rundb/dictofun/firmware/src/targets/dictofun/tasks/systemstate/task_state.h

// SPDX-License-Identifier:  Apache-2.0
/*
 * Copyright (c) 2022, Roman Turkin
 */
#pragma once

#include "FreeRTOS.h"
#include "boards.h"
#include "queue.h"
#include "timers.h"

#include "nvconfig.h"

namespace systemstate
{
void task_system_state(void* context);

// Set of states that define high-level behavior of the system. 
// Basically corresponds to the particular indication colors.
enum class SystemState: uint8_t
{
    INIT = 0,
    BATTERY_LOW = 1,
    DEVELOPMENT_MODE = 2,
    RECORD_PREPARE = 3,
    RECORDING = 4,
    RECORD_END = 5,
    BLE_OPERATION = 6,
    OUT_OF_MEMORY = 16,
    MEMORY_IS_CORRUPT = 17,
    SHUTDOWN = 32
};

struct Context
{
    QueueHandle_t cli_commands_handle{nullptr};
    QueueHandle_t cli_status_handle{nullptr};

    QueueHandle_t audio_commands_handle{nullptr};
    QueueHandle_t audio_status_handle{nullptr};

    QueueHandle_t memory_commands_handle{nullptr};
    QueueHandle_t memory_status_handle{nullptr};
    QueueHandle_t memory_event_handle{nullptr};

    QueueHandle_t audio_tester_commands_handle{nullptr};

    QueueHandle_t ble_commands_handle{nullptr};
    QueueHandle_t ble_requests_handle{nullptr};
    QueueHandle_t ble_keepalive_handle{nullptr};

    QueueHandle_t led_commands_handle{nullptr};

    QueueHandle_t button_events_handle{nullptr};
    QueueHandle_t button_requests_handle{nullptr};
    QueueHandle_t button_response_handle{nullptr};

    QueueHandle_t battery_measurements_handle{nullptr};
    QueueHandle_t battery_level_to_ble_handle{nullptr};

    TimerHandle_t record_timer_handle{nullptr};

    bool is_record_active{false};
    bool should_record_be_stored{false};
    bool is_ble_system_active{false};
    bool is_shutdown_demanded{false};
    bool is_battery_low{false};
    bool has_operation_timeout_expired{false};

    enum class MemoryStatus
    {
        BUSY,
        READY,
        OUT_OF_MEMORY,
        CORRUPT,
    };
    MemoryStatus memory_status{MemoryStatus::BUSY};

    // This variable tracks the use-case of a record restart before the session end
    uint32_t records_per_launch_counter{0};

    SystemState system_state{SystemState::INIT};

    struct Timestamps
    {
        uint32_t last_record_start_timestamp{timestamp_uninitialized_value};
        uint32_t last_record_end_timestamp{0};
        uint32_t last_ble_activity_timestamp{timestamp_uninitialized_value};
        uint32_t ble_disconnect_event_timestamp{timestamp_uninitialized_value};
        uint32_t shutdown_procedure_start_timestamp{timestamp_uninitialized_value};
        uint32_t low_battery_detected_timestamp{timestamp_uninitialized_value};
        uint32_t memory_issue_detected_timestamp{timestamp_uninitialized_value};

        bool has_start_timestamp_been_updated()
        {
            return last_record_start_timestamp != timestamp_uninitialized_value;
        }
        bool has_disconnect_timestamp_been_updated()
        {
            return ble_disconnect_event_timestamp != timestamp_uninitialized_value;
        }
        bool has_ble_timestamp_been_updated()
        {
            return last_ble_activity_timestamp != timestamp_uninitialized_value;
        }
        bool has_low_batt_detection_timestamp_been_updated()
        {
            return low_battery_detected_timestamp != timestamp_uninitialized_value;
        }
        bool has_memory_issue_detection_timestamp_been_updated()
        {
            return memory_issue_detected_timestamp != timestamp_uninitialized_value;
        }
        void reset()
        {
            last_ble_activity_timestamp = timestamp_uninitialized_value;
            ble_disconnect_event_timestamp = timestamp_uninitialized_value;
        }

    private:
        static constexpr uint32_t timestamp_uninitialized_value{0xaf1bfb98};
    };
    Timestamps timestamps;
};

void record_end_callback(TimerHandle_t timer);

void launch_cli_command_record(Context& context,
                               const uint32_t duration,
                               bool should_store_the_record);
void launch_cli_command_memory_test(Context& context, const uint32_t test_id, const uint32_t range_start, const uint32_t range_end);
void launch_cli_command_ble_operation(Context& context, const uint32_t command_id);
void launch_cli_command_system(Context& context, const uint32_t command_id);
void launch_cli_command_opmode(Context& context,
                               const uint32_t mode_id,
                               application::NvConfig& nvc);
void launch_cli_command_led(Context& context, const uint32_t color_id, const uint32_t mode_id);

void load_nvconfig(Context& context);
application::Mode get_operation_mode();
bool is_record_start_by_cli_allowed(Context& context);
result::Result launch_record_timer(const TickType_t record_duration, Context& context);

void shutdown_ldo();
void configure_power_latch();
bool process_timeouts(Context& context);
result::Result enable_ble_subsystem(Context& context);
result::Result disable_ble_subsystem(Context& context);

result::Result request_record_creation(const Context& context);
result::Result request_record_start(Context& context);
result::Result request_record_stop(const Context& context);
result::Result request_record_closure(const Context& context);

} // namespace systemstate
