rundb/dictofun/firmware/src/targets/dictofun/BleSystem.cpp

// SPDX-License-Identifier:  Apache-2.0
/*
 * Copyright (c) 2022, Roman Turkin
 */

#include "BleSystem.h"
#include <softdevice/common/nrf_sdh.h>
#include <softdevice/common/nrf_sdh_ble.h>
#include <ble/nrf_ble_qwr/nrf_ble_qwr.h>
#include <ble/nrf_ble_gatt/nrf_ble_gatt.h>
#include <ble/ble_services/ble_lbs/ble_lbs.h>
#include <ble/common/ble_advdata.h>
#include <ble/common/ble_conn_params.h>
#include <ble/peer_manager/peer_manager_handler.h>
#include <libraries/util/app_error.h>
#include "ble_file_transfer_service.h"
#include <nrf_log.h>
#include <stdint.h>
#include "BleServices.h"
#include <boards/boards.h>
#include "simple_fs.h"

// Legacy define. I haven't come up with a replacement for this part of nordic interfaces
// NRF_BLE_QWR_DEF(m_qwr);
//BLE_LBS_DEF(m_lbs);                                                             /**< LED Button Service instance. */
BLE_FTS_DEF(m_fts, NRF_SDH_BLE_TOTAL_LINK_COUNT);

#define APP_ADV_INTERVAL                200                                      /**< The advertising interval (in units of 0.625 ms; this value corresponds to 40 ms). */
#define APP_ADV_DURATION                BLE_GAP_ADV_TIMEOUT_GENERAL_UNLIMITED   /**< The advertising time-out (in units of seconds). When set to 0, we will never time out. */

static uint8_t m_enc_advdata[BLE_GAP_ADV_SET_DATA_SIZE_MAX];                    /**< Buffer for storing an encoded advertising set. */
static uint8_t m_enc_scan_response_data[BLE_GAP_ADV_SET_DATA_SIZE_MAX];         /**< Buffer for storing an encoded scan data. */
static uint8_t m_adv_handle = BLE_GAP_ADV_SET_HANDLE_NOT_SET;                   /**< Advertising handle used to identify an advertising set. */

static ble_gap_adv_data_t m_adv_data =
{
    .adv_data =
    {
        .p_data = m_enc_advdata,
        .len    = BLE_GAP_ADV_SET_DATA_SIZE_MAX
    },
    .scan_rsp_data =
    {
        .p_data = m_enc_scan_response_data,
        .len    = BLE_GAP_ADV_SET_DATA_SIZE_MAX

    }
};

static nrf_ble_gatt_t m_gatt;
NRF_SDH_BLE_OBSERVER(m_gatt_obs, NRF_BLE_GATT_BLE_OBSERVER_PRIO, nrf_ble_gatt_on_ble_evt, &m_gatt);


namespace ble
{

BleSystem * BleSystem::_instance{nullptr};
const char BleSystem::DEVICE_NAME[] = BOARD_NAME;

static void services_init();
static void advertising_init();

void BleSystem::init()
{
    initBleStack();
    initGapParams();
    initGatt();
    initBonding();
    _bleServices.init();
    _qwr_default_handle = _bleServices.getQwrHandle();
    advertising_init();
    initConnParameters();
}

void BleSystem::start()
{
    _bleServices.start();
    startAdvertising();
    _isActive = true;
}

void BleSystem::stop()
{
    const auto disconnect_result = sd_ble_gap_disconnect(BleSystem::getInstance().getConnectionHandle(), 
        BLE_HCI_REMOTE_USER_TERMINATED_CONNECTION);
    if (disconnect_result != 0)
    {
        NRF_LOG_WARNING("gap disconnect: err_code = 0x%x", disconnect_result);
    }
    stopAdvertising();
    _isActive = false;
}

void BleSystem::cyclic()
{
    if (_isActive)
    {
        _bleServices.cyclic();
    }
}

void BleSystem::startAdvertising()
{
    ret_code_t           err_code;

    err_code = sd_ble_gap_adv_start(m_adv_handle, APP_BLE_CONN_CFG_TAG);
    //APP_ERROR_CHECK(err_code);
    if (err_code != 0)
    {
        NRF_LOG_WARNING("startAdv: err_code = %d", err_code);
    }
}

void BleSystem::stopAdvertising()
{
    ret_code_t           err_code;

    err_code = sd_ble_gap_adv_stop(m_adv_handle);
    if (err_code != 0)
    {
        NRF_LOG_WARNING("stopAdv: err_code = %d", err_code);
    }
}

void ble_evt_handler(ble_evt_t const * p_ble_evt, void * p_context)
{
    BleSystem::getInstance().bleEventHandler(p_ble_evt, p_context);
}

void BleSystem::bleEventHandler(ble_evt_t const * p_ble_evt, void * p_context)
{
    ret_code_t err_code;
   
    switch (p_ble_evt->header.evt_id)
    {
        case BLE_GAP_EVT_CONNECTED:
            NRF_LOG_INFO("Connected");
            // bsp_board_led_on(CONNECTED_LED);
            // bsp_board_led_off(ADVERTISING_LED);
            m_conn_handle = p_ble_evt->evt.gap_evt.conn_handle;
            err_code = nrf_ble_qwr_conn_handle_assign(_qwr_default_handle, m_conn_handle);
            APP_ERROR_CHECK(err_code);
            break;

        case BLE_GAP_EVT_DISCONNECTED:
            NRF_LOG_INFO("Disconnected");
            //bsp_board_led_off(CONNECTED_LED);
            m_conn_handle = BLE_CONN_HANDLE_INVALID;
            startAdvertising();
            break;

        case BLE_GAP_EVT_SEC_PARAMS_REQUEST:
            NRF_LOG_DEBUG("BLE_GAP_EVT_SEC_PARAMS_REQUEST");
            break;
        
        case BLE_GAP_EVT_AUTH_KEY_REQUEST:
            NRF_LOG_INFO("BLE_GAP_EVT_AUTH_KEY_REQUEST");
            break;

        case BLE_GAP_EVT_LESC_DHKEY_REQUEST:
            NRF_LOG_INFO("BLE_GAP_EVT_LESC_DHKEY_REQUEST");
            break;
       case BLE_GAP_EVT_AUTH_STATUS:
            NRF_LOG_INFO("BLE_GAP_EVT_AUTH_STATUS: status=0x%x bond=0x%x lv4: %d kdist_own:0x%x kdist_peer:0x%x",
                          p_ble_evt->evt.gap_evt.params.auth_status.auth_status,
                          p_ble_evt->evt.gap_evt.params.auth_status.bonded,
                          p_ble_evt->evt.gap_evt.params.auth_status.sm1_levels.lv4,
                          *((uint8_t *)&p_ble_evt->evt.gap_evt.params.auth_status.kdist_own),
                          *((uint8_t *)&p_ble_evt->evt.gap_evt.params.auth_status.kdist_peer));
            break;

        case BLE_GAP_EVT_PHY_UPDATE_REQUEST:
        {
            NRF_LOG_DEBUG("PHY update request.");
            ble_gap_phys_t const phys =
            {
                .tx_phys = BLE_GAP_PHY_AUTO,
                .rx_phys = BLE_GAP_PHY_AUTO,
            };
            err_code = sd_ble_gap_phy_update(p_ble_evt->evt.gap_evt.conn_handle, &phys);
            APP_ERROR_CHECK(err_code);
        } break;

        case BLE_GATTS_EVT_SYS_ATTR_MISSING:
            // No system attributes have been stored.
            err_code = sd_ble_gatts_sys_attr_set(m_conn_handle, NULL, 0, 0);
            APP_ERROR_CHECK(err_code);
            break;

        case BLE_GATTC_EVT_TIMEOUT:
            // Disconnect on GATT Client timeout event.
            NRF_LOG_DEBUG("GATT Client Timeout.");
            err_code = sd_ble_gap_disconnect(p_ble_evt->evt.gattc_evt.conn_handle,
                                             BLE_HCI_REMOTE_USER_TERMINATED_CONNECTION);
            APP_ERROR_CHECK(err_code);
            break;

        case BLE_GATTS_EVT_TIMEOUT:
            // Disconnect on GATT Server timeout event.
            NRF_LOG_DEBUG("GATT Server Timeout.");
            err_code = sd_ble_gap_disconnect(p_ble_evt->evt.gatts_evt.conn_handle,
                                             BLE_HCI_REMOTE_USER_TERMINATED_CONNECTION);
            APP_ERROR_CHECK(err_code);
            break;

        default:
            // No implementation needed.
            break;
    }
}

void BleSystem::initBleStack()
{
    ret_code_t err_code;

    err_code = nrf_sdh_enable_request();
    APP_ERROR_CHECK(err_code);

    // Configure the BLE stack using the default settings.
    // Fetch the start address of the application RAM.
    uint32_t ram_start = 0;
    err_code = nrf_sdh_ble_default_cfg_set(APP_BLE_CONN_CFG_TAG, &ram_start);
    APP_ERROR_CHECK(err_code);

    // Enable BLE stack.
    err_code = nrf_sdh_ble_enable(&ram_start);
    APP_ERROR_CHECK(err_code);

    // Register a handler for BLE events.
    NRF_SDH_BLE_OBSERVER(m_ble_observer, APP_BLE_OBSERVER_PRIO, ble_evt_handler, NULL);    
}

void BleSystem::initGapParams()
{
    ret_code_t              err_code;
    ble_gap_conn_params_t   gap_conn_params;
    ble_gap_conn_sec_mode_t sec_mode;

    BLE_GAP_CONN_SEC_MODE_SET_OPEN(&sec_mode);

    err_code = sd_ble_gap_device_name_set(&sec_mode,
                                          (const uint8_t *)DEVICE_NAME,
                                          strlen(DEVICE_NAME));
    APP_ERROR_CHECK(err_code);

    memset(&gap_conn_params, 0, sizeof(gap_conn_params));

    gap_conn_params.min_conn_interval = MIN_CONN_INTERVAL;
    gap_conn_params.max_conn_interval = MAX_CONN_INTERVAL;
    gap_conn_params.slave_latency     = SLAVE_LATENCY;
    gap_conn_params.conn_sup_timeout  = CONN_SUP_TIMEOUT;

    err_code = sd_ble_gap_ppcp_set(&gap_conn_params);
    APP_ERROR_CHECK(err_code);
}

void BleSystem::initGatt()
{
    ret_code_t err_code = nrf_ble_gatt_init(&m_gatt, NULL);
    APP_ERROR_CHECK(err_code);
}

void BleSystem::bonded_client_add(pm_evt_t const * p_evt)
{
    uint16_t   conn_handle = p_evt->conn_handle;
    uint16_t   peer_id     = p_evt->peer_id;
}

void BleSystem::bonded_client_remove_all()
{
    // TODO: implement
}

void BleSystem::on_bonded_peer_reconnection_lvl_notify(pm_evt_t const * p_evt)
{
    ret_code_t        err_code;
    static uint16_t   peer_id   = PM_PEER_ID_INVALID;

    peer_id = p_evt->peer_id;
}

void BleSystem::pm_evt_handler(pm_evt_t const * p_evt)
{
    pm_handler_on_pm_evt(p_evt);
    pm_handler_disconnect_on_sec_failure(p_evt);
    pm_handler_flash_clean(p_evt);

    switch (p_evt->evt_id)
    {
        case PM_EVT_BONDED_PEER_CONNECTED:
            bonded_client_add(p_evt);
            on_bonded_peer_reconnection_lvl_notify(p_evt);
            break;

        case PM_EVT_CONN_SEC_SUCCEEDED:
            bonded_client_add(p_evt);
            break;

        case PM_EVT_PEERS_DELETE_SUCCEEDED:
            bonded_client_remove_all();

            // Bonds are deleted. Start scanning.
            break;

        default:
            break;
    }
}

void BleSystem::initBonding()
{
    ble_gap_sec_params_t sec_param;
    ret_code_t           err_code;

    err_code = pm_init();
    APP_ERROR_CHECK(err_code);

    memset(&sec_param, 0, sizeof(ble_gap_sec_params_t));

    // Security parameters to be used for all security procedures.
    sec_param.bond           = SEC_PARAM_BOND;
    sec_param.mitm           = SEC_PARAM_MITM;
    sec_param.lesc           = SEC_PARAM_LESC;
    sec_param.keypress       = SEC_PARAM_KEYPRESS;
    sec_param.io_caps        = SEC_PARAM_IO_CAPABILITIES;
    sec_param.oob            = SEC_PARAM_OOB;
    sec_param.min_key_size   = SEC_PARAM_MIN_KEY_SIZE;
    sec_param.max_key_size   = SEC_PARAM_MAX_KEY_SIZE;
    sec_param.kdist_own.enc  = 1;
    sec_param.kdist_own.id   = 1;
    sec_param.kdist_peer.enc = 1;
    sec_param.kdist_peer.id  = 1;

    err_code = pm_sec_params_set(&sec_param);
    APP_ERROR_CHECK(err_code);

    err_code = pm_register(pm_evt_handler);
    APP_ERROR_CHECK(err_code);
}

static void on_conn_params_evt(ble_conn_params_evt_t * p_evt)
{
    ret_code_t err_code;

    if (p_evt->evt_type == BLE_CONN_PARAMS_EVT_FAILED)
    {
        err_code = sd_ble_gap_disconnect(BleSystem::getInstance().getConnectionHandle(), 
                                        BLE_HCI_CONN_INTERVAL_UNACCEPTABLE);
        APP_ERROR_CHECK(err_code);
    }
}

static void conn_params_error_handler(uint32_t nrf_error)
{
    APP_ERROR_HANDLER(nrf_error);
}

void BleSystem::initConnParameters()
{
    ret_code_t             err_code;
    ble_conn_params_init_t cp_init;

    memset(&cp_init, 0, sizeof(cp_init));

    cp_init.p_conn_params                  = NULL;
    cp_init.first_conn_params_update_delay = FIRST_CONN_PARAMS_UPDATE_DELAY;
    cp_init.next_conn_params_update_delay  = NEXT_CONN_PARAMS_UPDATE_DELAY;
    cp_init.max_conn_params_update_count   = MAX_CONN_PARAMS_UPDATE_COUNT;
    cp_init.start_on_notify_cccd_handle    = BLE_GATT_HANDLE_INVALID;
    cp_init.disconnect_on_fail             = false;
    cp_init.evt_handler                    = on_conn_params_evt;
    cp_init.error_handler                  = conn_params_error_handler;

    err_code = ble_conn_params_init(&cp_init);
    APP_ERROR_CHECK(err_code);
}

static void nrf_qwr_error_handler(uint32_t nrf_error)
{
    APP_ERROR_HANDLER(nrf_error);
}

void advertising_init(void)
{
    ret_code_t    err_code;
    ble_advdata_t advdata;
    ble_advdata_t srdata;

    static const size_t MAX_UUIDS_COUNT = 3U;
    ble_uuid_t adv_uuids[MAX_UUIDS_COUNT];
    const auto uuids_count = BleSystem::getInstance().getServices().setAdvUuids(adv_uuids, MAX_UUIDS_COUNT);
    

    // Build and set advertising data.
    memset(&advdata, 0, sizeof(advdata));

    advdata.name_type          = BLE_ADVDATA_FULL_NAME;
    advdata.include_appearance = true;
    advdata.flags              = BLE_GAP_ADV_FLAGS_LE_ONLY_GENERAL_DISC_MODE;
    advdata.uuids_complete.uuid_cnt = uuids_count;
    advdata.uuids_complete.p_uuids = adv_uuids;

    memset(&srdata, 0, sizeof(srdata));
    srdata.uuids_complete.uuid_cnt = uuids_count;
    srdata.uuids_complete.p_uuids  = adv_uuids;

    err_code = ble_advdata_encode(&advdata, m_adv_data.adv_data.p_data, &m_adv_data.adv_data.len);
    APP_ERROR_CHECK(err_code);

    err_code = ble_advdata_encode(&srdata, m_adv_data.scan_rsp_data.p_data, &m_adv_data.scan_rsp_data.len);
    APP_ERROR_CHECK(err_code);

    ble_gap_adv_params_t adv_params;

    // Set advertising parameters.
    memset(&adv_params, 0, sizeof(adv_params));

    adv_params.primary_phy     = BLE_GAP_PHY_1MBPS;
    adv_params.duration        = APP_ADV_DURATION;
    adv_params.properties.type = BLE_GAP_ADV_TYPE_CONNECTABLE_SCANNABLE_UNDIRECTED;
    adv_params.p_peer_addr     = NULL;
    adv_params.filter_policy   = BLE_GAP_ADV_FP_ANY;
    adv_params.interval        = APP_ADV_INTERVAL;

    err_code = sd_ble_gap_adv_set_configure(&m_adv_handle, &m_adv_data, &adv_params);
    APP_ERROR_CHECK(err_code);
}

}
