rundb/dictofun/firmware/src/targets/dictofun/app_error_handler.cpp

// SPDX-License-Identifier:  Apache-2.0
/*
 * Copyright (c) 2023, Roman Turkin
 */
#include "nrf_log.h"
#include "nrf_log_ctrl.h"
#include "nrf_sdm.h"
#include <boards.h>
#include <nrf_gpio.h>

#include "FreeRTOS.h"
#include "task.h"

extern "C" void vApplicationStackOverflowHook(TaskHandle_t xTask, char* pcTaskName)
{
    NRF_LOG_ERROR("STACK OVERFLOW DETECTED: %s", pcTaskName);
}

void app_error_fault_handler(uint32_t id, uint32_t pc, uint32_t info)
{
    __disable_irq();
    NRF_LOG_FINAL_FLUSH();

#ifndef DEBUG
    NRF_LOG_ERROR("Fatal error");
#else
    switch(id)
    {
#    if defined(SOFTDEVICE_PRESENT) && SOFTDEVICE_PRESENT
    case NRF_FAULT_ID_SD_ASSERT:
        NRF_LOG_ERROR("SOFTDEVICE: ASSERTION FAILED");
        break;
    case NRF_FAULT_ID_APP_MEMACC:
        NRF_LOG_ERROR("SOFTDEVICE: INVALID MEMORY ACCESS");
        break;
#    endif
    case NRF_FAULT_ID_SDK_ASSERT: {
        assert_info_t* p_info = (assert_info_t*)info;
        NRF_LOG_ERROR("ASSERTION FAILED at %s:%u", p_info->p_file_name, p_info->line_num);
        break;
    }
    case NRF_FAULT_ID_SDK_ERROR: {
        error_info_t* p_info = (error_info_t*)info;
        NRF_LOG_ERROR("ERROR %u [%s] at %s:%u\r\nPC at: 0x%08x",
                      p_info->err_code,
                      nrf_strerror_get(p_info->err_code),
                      p_info->p_file_name,
                      p_info->line_num,
                      pc);
        NRF_LOG_ERROR("End of error report");
        break;
    }
    default:
        NRF_LOG_ERROR("UNKNOWN FAULT at 0x%08X", pc);
        break;
    }
#endif

    NRF_BREAKPOINT_COND;
    // On assert, the system can only recover with a reset.

    //nrf_gpio_pin_clear(LDO_EN_PIN);
    nrf_gpio_pin_clear(LDO_LATCH_D_PIN);
    nrf_gpio_pin_set(LDO_LATCH_CLK_PIN);
    for (volatile int i = 0; i < 100000; ++i);
    nrf_gpio_pin_clear(LDO_LATCH_CLK_PIN);
    for (volatile int i = 0; i < 100000; ++i);
    nrf_gpio_pin_set(LDO_LATCH_CLK_PIN);
}
