rundb/dictofun/firmware/src/targets/bootloader/main.c

/**
 * Copyright (c) 2016 - 2021, Nordic Semiconductor ASA
 *
 * All rights reserved.
 *
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
 * 3. Neither the name of Nordic Semiconductor ASA nor the names of its
 *    contributors may be used to endorse or promote products derived from this
 *    software without specific prior written permission.
 *
 * 4. This software, with or without modification, must only be used with a
 *    Nordic Semiconductor ASA integrated circuit.
 *
 * 5. Any software provided in binary form under this license must not be reverse
 *    engineered, decompiled, modified and/or disassembled.
 *
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
 */
/** @file
 *
 * @defgroup bootloader_secure_ble main.c
 * @{
 * @ingroup dfu_bootloader_api
 * @brief Bootloader project main file for secure DFU.
 *
 */

#include <stdint.h>
#include "boards.h"
#include "nrf_mbr.h"
#include "nrf_bootloader.h"
#include "nrf_bootloader_app_start.h"
#include "nrf_bootloader_dfu_timers.h"
#include "nrf_dfu.h"
#include "nrf_log.h"
#include "nrf_log_ctrl.h"
#include "nrf_log_default_backends.h"
#include "app_error.h"
#include "app_error_weak.h"
#include "nrf_bootloader_info.h"
#include "nrf_delay.h"

static void on_error(void)
{
    NRF_LOG_FINAL_FLUSH();

#if NRF_MODULE_ENABLED(NRF_LOG_BACKEND_RTT)
    // To allow the buffer to be flushed by the host.
    nrf_delay_ms(100);
#endif
#ifdef NRF_DFU_DEBUG_VERSION
    NRF_BREAKPOINT_COND;
#endif
    NVIC_SystemReset();
}


void app_error_handler(uint32_t error_code, uint32_t line_num, const uint8_t * p_file_name)
{
    NRF_LOG_ERROR("%s:%d", p_file_name, line_num);
    on_error();
}


void app_error_fault_handler(uint32_t id, uint32_t pc, uint32_t info)
{
    __disable_irq();
    NRF_LOG_FINAL_FLUSH();

#ifndef DEBUG
    NRF_LOG_ERROR("Fatal error");
#else
    switch(id)
    {
#    if defined(SOFTDEVICE_PRESENT) && SOFTDEVICE_PRESENT
    case NRF_FAULT_ID_SD_ASSERT:
        NRF_LOG_ERROR("SOFTDEVICE: ASSERTION FAILED");
        break;
    case NRF_FAULT_ID_APP_MEMACC:
        NRF_LOG_ERROR("SOFTDEVICE: INVALID MEMORY ACCESS");
        break;
#    endif
    case NRF_FAULT_ID_SDK_ASSERT: {
        assert_info_t* p_info = (assert_info_t*)info;
        NRF_LOG_ERROR("ASSERTION FAILED at %s:%u", p_info->p_file_name, p_info->line_num);
        break;
    }
    case NRF_FAULT_ID_SDK_ERROR: {
        error_info_t* p_info = (error_info_t*)info;
        NRF_LOG_ERROR("ERROR %u [%s] at %s:%u\r\nPC at: 0x%08x",
                      p_info->err_code,
                      nrf_strerror_get(p_info->err_code),
                      p_info->p_file_name,
                      p_info->line_num,
                      pc);
        NRF_LOG_ERROR("End of error report");
        break;
    }
    default:
        NRF_LOG_ERROR("UNKNOWN FAULT at 0x%08X", pc);
        break;
    }
#endif

    NRF_BREAKPOINT_COND;
    // On assert, the system can only recover with a reset.

    on_error();
}


void app_error_handler_bare(uint32_t error_code)
{
    NRF_LOG_ERROR("Received an error: 0x%08x!", error_code);
    on_error();
}

/**
 * @brief Function notifies certain events in DFU process.
 */
static void dfu_observer(nrf_dfu_evt_type_t evt_type)
{
    switch (evt_type)
    {
        case NRF_DFU_EVT_DFU_FAILED:
        case NRF_DFU_EVT_DFU_ABORTED:
        case NRF_DFU_EVT_DFU_INITIALIZED:
            bsp_board_init(BSP_INIT_LEDS);
            bsp_board_led_on(BSP_BOARD_LED_0);
            bsp_board_led_on(BSP_BOARD_LED_1);
            bsp_board_led_off(BSP_BOARD_LED_2);
            break;
        case NRF_DFU_EVT_TRANSPORT_ACTIVATED:
            bsp_board_led_off(BSP_BOARD_LED_1);
            bsp_board_led_on(BSP_BOARD_LED_2);
            break;
        case NRF_DFU_EVT_DFU_STARTED:
            break;
        default:
            break;
    }
}

// static constexpr uint8_t power_flipflop_clk{LDO_LATCH_CLK_PIN};
// static constexpr uint8_t power_flipflop_d{LDO_LATCH_D_PIN};

void configure_power_latch()
{
    nrf_gpio_cfg_output(LDO_LATCH_CLK_PIN);
    nrf_gpio_cfg_output(LDO_LATCH_D_PIN);

    nrf_gpio_pin_clear(LDO_LATCH_CLK_PIN);
    nrf_gpio_pin_set(LDO_LATCH_D_PIN);

    for (volatile int i = 0; i < 100000; ++i);
    nrf_gpio_pin_set(LDO_LATCH_CLK_PIN);
    for (volatile int i = 0; i < 100000; ++i);
    nrf_gpio_pin_clear(LDO_LATCH_CLK_PIN);
}

/**@brief Function for application main entry. */
int main(void)
{
    
    uint32_t ret_val;

    configure_power_latch();

    // Must happen before flash protection is applied, since it edits a protected page.
    nrf_bootloader_mbr_addrs_populate();

    // Protect MBR and bootloader code from being overwritten.
    ret_val = nrf_bootloader_flash_protect(0, MBR_SIZE);
    APP_ERROR_CHECK(ret_val);
    ret_val = nrf_bootloader_flash_protect(BOOTLOADER_START_ADDR, BOOTLOADER_SIZE);
    APP_ERROR_CHECK(ret_val);

    (void) NRF_LOG_INIT(nrf_bootloader_dfu_timer_counter_get);
    NRF_LOG_DEFAULT_BACKENDS_INIT();

    NRF_LOG_INFO("Inside main");

    ret_val = nrf_bootloader_init(dfu_observer);
    APP_ERROR_CHECK(ret_val);

    NRF_LOG_FLUSH();
 
    NRF_LOG_ERROR("After main, should never be reached.");
    NRF_LOG_FLUSH();

    APP_ERROR_CHECK_BOOL(false);
}

/**
 * @}
 */
