rundb/dictofun/firmware/test/dictofun_ble.py

import logging
import gatt
from enum import Enum
import time
import threading
from fts import FtsClient

"""
Class representing Dictofun as a GATT device. Instance of this class can be created when 
device is discovered with BLE.
It contains inherited methods of gatt.device related to connection states and to characteristics 
callbacks.
"""
class DictofunBle(gatt.Device):
    mac_address = None
    manager = None
    reconnect_attempts = 0
    reconnect_time = 1
    are_services_resolved = False
    reconnect_thread = None

    """
    Instance of FTS Client, shall be instantiated after services discovery and only if all
    FTS characteristics exist in the device.
    """
    fts = None

    def __init__(self, mac_address, manager):
        super().__init__(mac_address, manager)

    """
    This method should be used publicly in order to create an instance of a Dictofun using 
    an existing instance of a GATT device.
    """
    @classmethod
    def from_parent(cls, parent):
        return cls(parent.mac_address, parent.manager)

    """
    NB: Due to inheritance issues connect() and _connect() can't be used here
    """
    def connect_to_device(self, reconnect_attempts = 0):
        self.reconnect_attempts = reconnect_attempts + 1
        self._connect_to_device()

    def _connect_to_device(self):
        if self.reconnect_attempts > 0:
            super().connect()
            self.reconnect_attempts -= 1

    def wait_until_connected(self, timeout = 5):
        start_time = time.time()
        timeout_value = timeout
        while not self.is_connected() and time.time() - start_time < timeout_value:
            time.sleep(0.1)
        if time.time() - start_time > timeout_value:
            logging.error("connection failed")
            return -1
        return 0
    
    def wait_until_disconnected(self, timeout = 5):
        start_time = time.time()
        timeout_value = timeout
        while self.is_connected() and time.time() - start_time < timeout_value:
            time.sleep(0.1)
        if time.time() - start_time > timeout_value:
            logging.error("disconnect failed")
            return -1
        return 0

    def wait_until_services_resolved(self, timeout = 5):
        start_time = time.time()
        timeout_value = timeout
        while not self.are_services_resolved and time.time() - start_time < timeout_value:
            time.sleep(0.1)
        if time.time() - start_time > timeout_value:
            logging.error("services resolution failed")
            return -1
        self.fts = FtsClient(self)
        return 0

    """
    This call should be called from a separate thread context
    """
    def _reconnect(self):
        time.sleep(self.reconnect_time)
        logging.info("attempting reconnect")
        self._connect_to_device()

    def connect_succeeded(self):
        super().connect_succeeded()
        logging.debug("[%s] Connected" % (self.mac_address))

    def connect_failed(self, error):
        super().connect_failed(error)
        logging.debug("[%s] Connection failed: %s" % (self.mac_address, str(error)))
        if self.reconnect_attempts > 0:
            logging.info("reconnect shall be attempted in %d seconds" % self.reconnect_time)
            reconnect_thread = threading.Thread(target=self._reconnect)
            reconnect_thread.start()

    def disconnect_succeeded(self):
        super().disconnect_succeeded()
        logging.debug("[%s] Disconnected" % (self.mac_address))
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
